abellol/Dispositivo_MIGUEL/Evidencias/Esquematico PCB.png

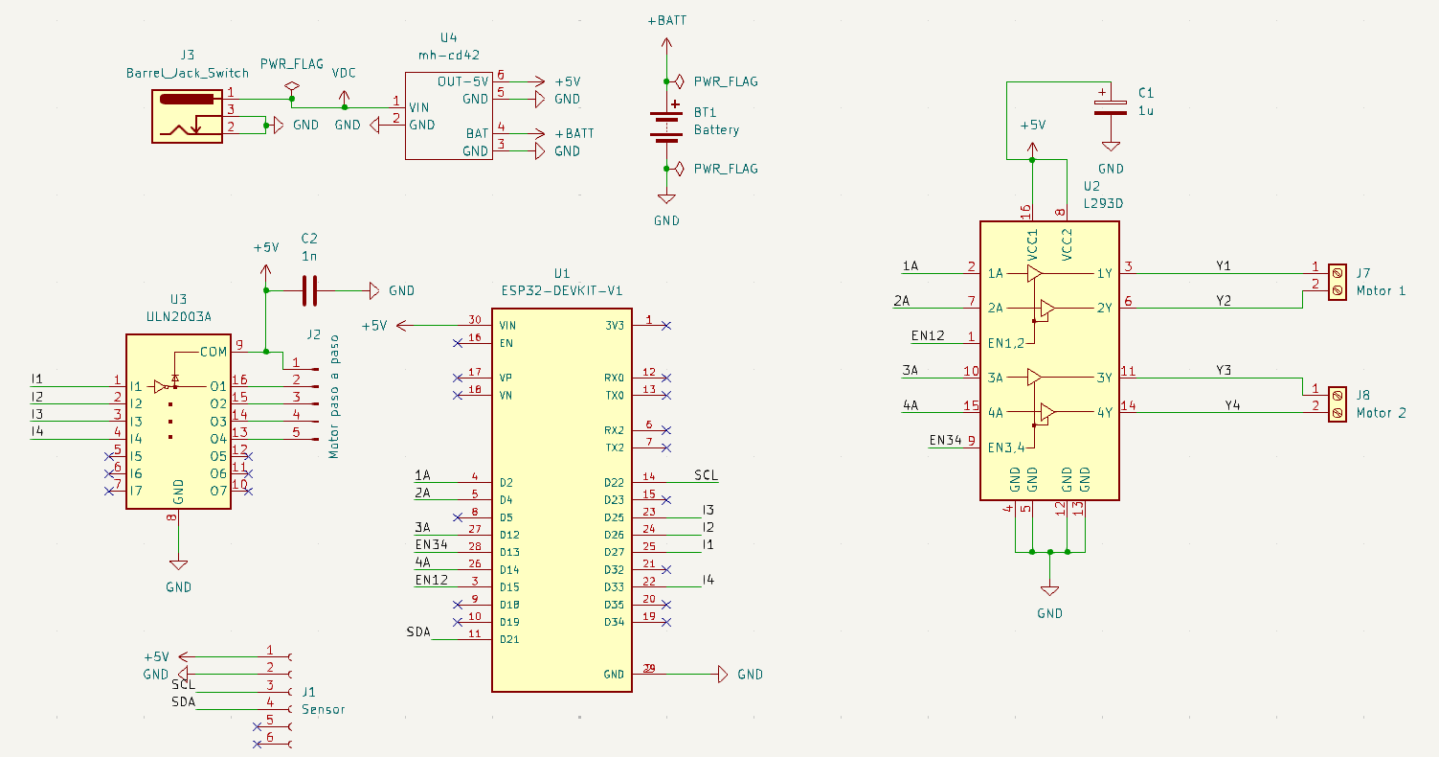
Evidencias/Esquematico PCB.png
