abellol/Dispositivo_MIGUEL/Evidencias/Miguel Roadmap.png

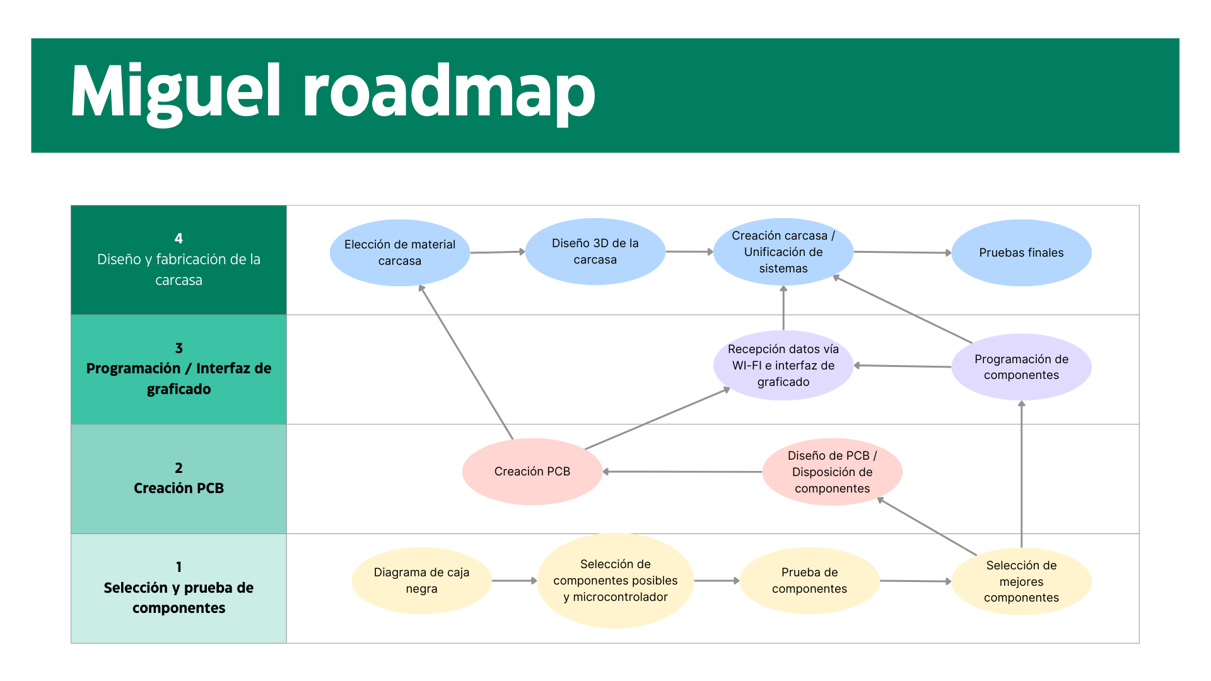
Evidencias/Miguel Roadmap.png
