abellol/Dispositivo_MIGUEL/Evidencias/MIGUEL_montado.jpg

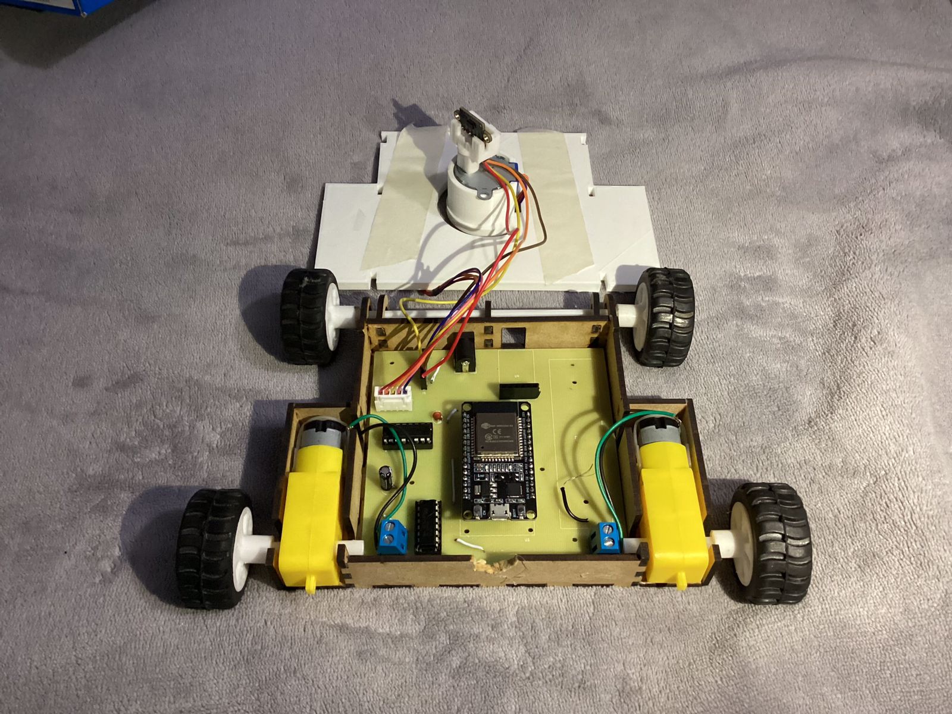
Evidencias/MIGUEL_montado.jpg
