abellol/Dispositivo_MIGUEL/Evidencias/multimeter.jpg

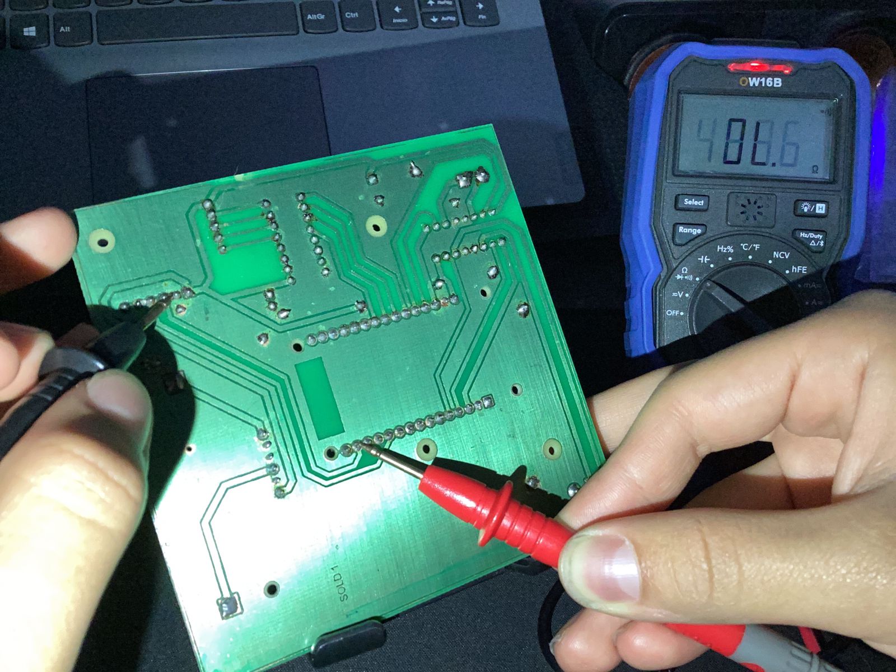
Evidencias/multimeter.jpg
