abellol/Dispositivo_MIGUEL/Evidencias/pcb_real.jpg

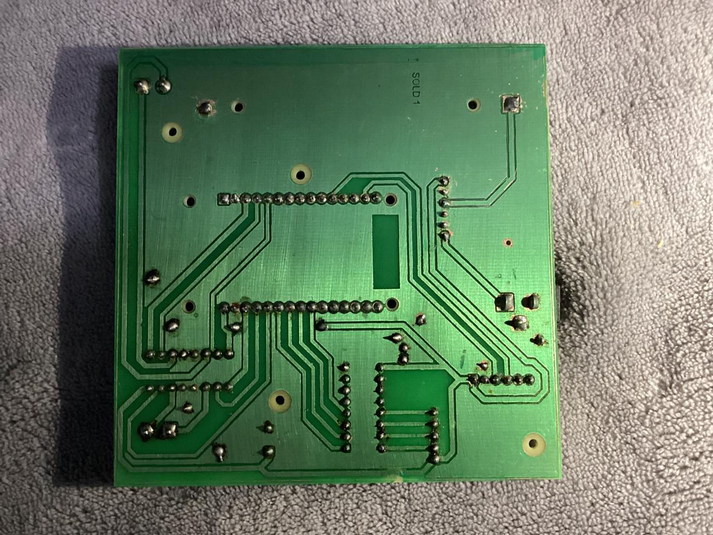
Evidencias/pcb_real.jpg
