abellol/Dispositivo_MIGUEL/Evidencias/ruteo pcb.png

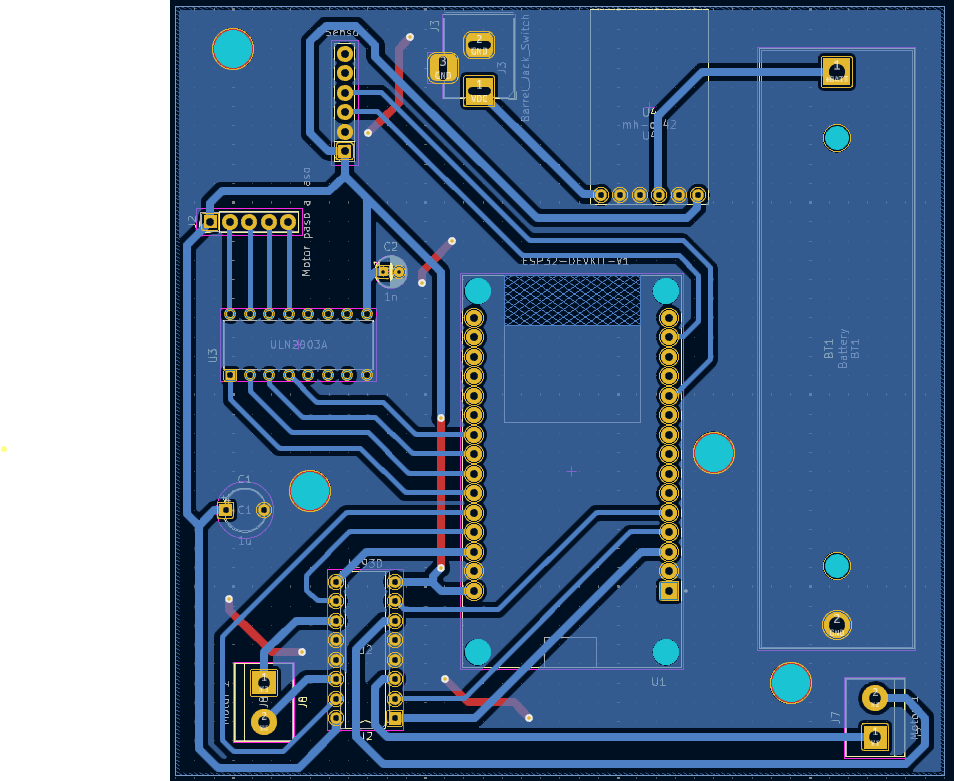
Evidencias/ruteo pcb.png
