abellol/Dispositivo_MIGUEL/Evidencias/vista_1_MIGUEL.png

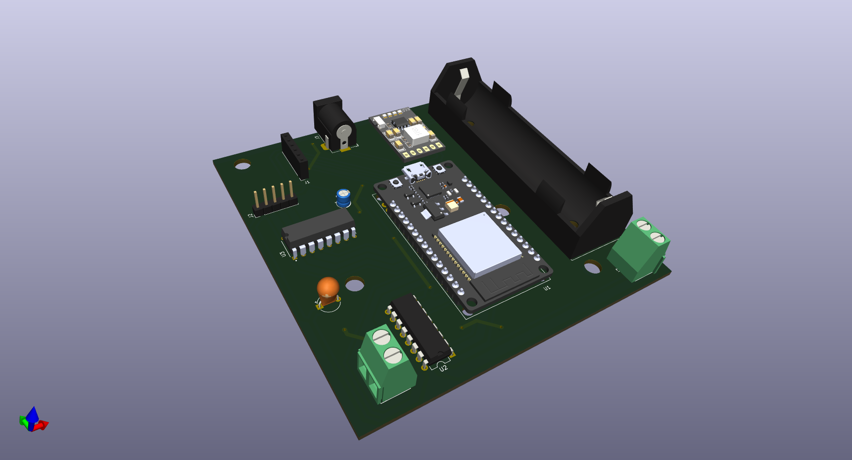
Evidencias/vista_1_MIGUEL.png
